Cipulot/CDS/PCB/CDS.kicad_sch

## KiCad design PCB/CDS.kicad_sch (2024-03-03)

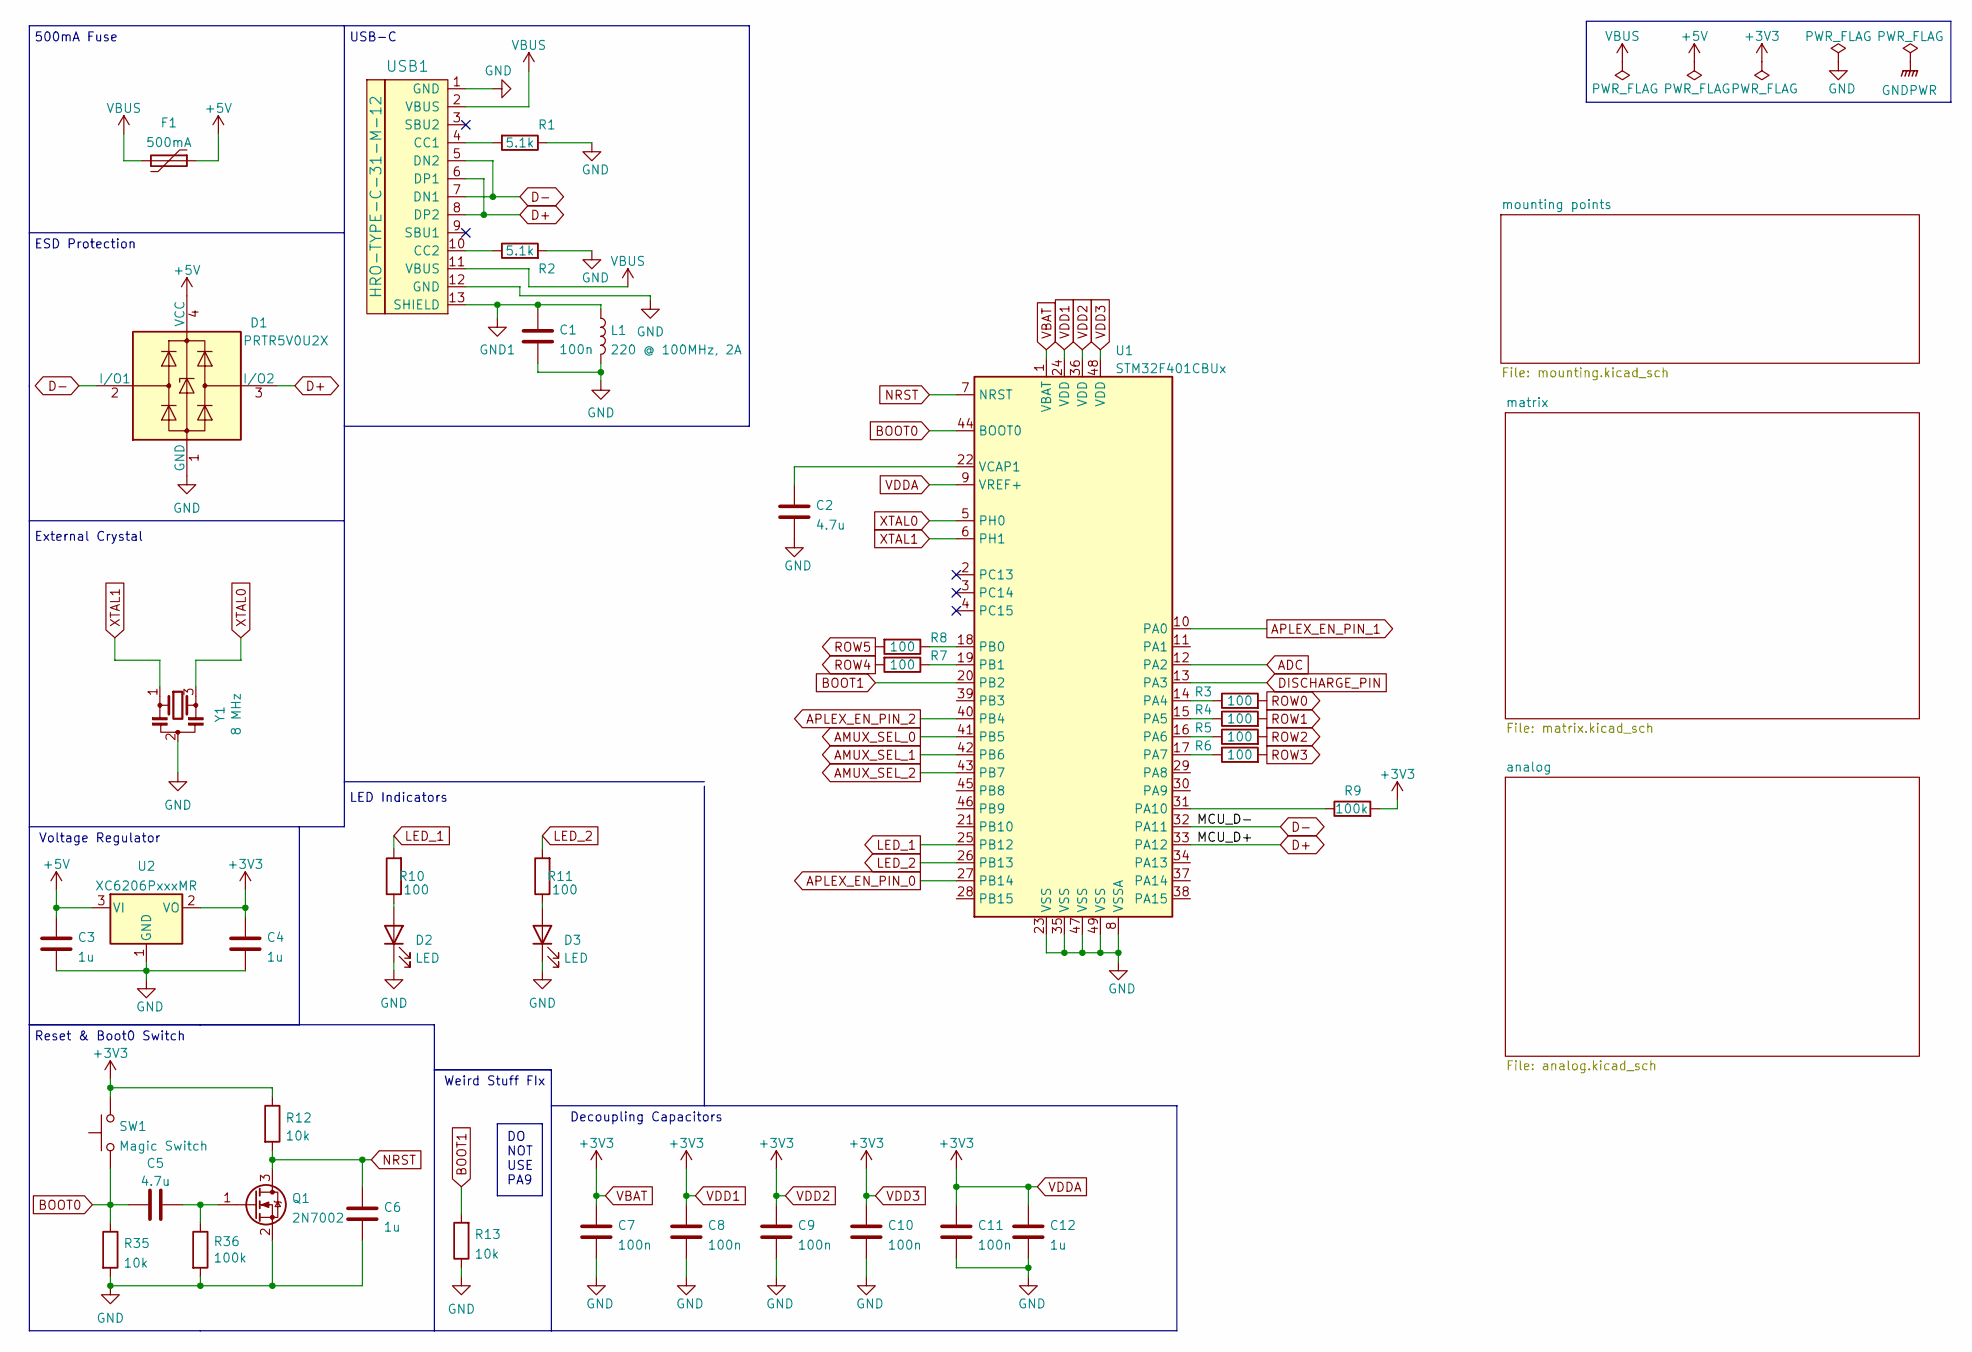
[picture p6: schematic CDS.kicad_sch]

Parts:
C1, C7, C8, C9, C10, C11: 100n; C_0402_1005Metric; LCSC C307331
C2, C5: 4.7u; C_0402_1005Metric; LCSC C23733
C3, C4, C6, C12: 1u; C_0402_1005Metric; LCSC C52923
D1: PRTR5V0U2X; SOT-143; LCSC C2827688
D2, D3: LED; LED_D3.0mm
F1: 500mA; Fuse_0603_1608Metric; LCSC C720073
L1: 220 @ 100MHz, 2A; L_0603_1608Metric; LCSC C85832
Q1: 2N7002; SOT-23; LCSC C8545
R1, R2: 5.1k; R_0402_1005Metric; LCSC C25905
R3, R4, R5, R6, R7, R8, R10, R11: 100; R_0402_1005Metric; LCSC C25076
R9, R36: 100k; R_0402_1005Metric; LCSC C25741
R12, R13, R35: 10k; R_0402_1005Metric; LCSC C25744
SW1: Magic Switch; SW_SPST_TL3342; LCSC C318884
U1: STM32F401CBUx; QFN-48-1EP_7x7mm_P0.5mm_EP5.6x5.6mm; LCSC C118825
U2: XC6206PxxxMR; SOT-23; LCSC C5446
USB1: HRO-TYPE-C-31-M-12; HRO-TYPE-C-31-M-12-Assembly; LCSC C165948
Y1: 8 MHz; Resonator_SMD_Murata_CSTxExxV-3Pin_3.0x1.1mm; LCSC C907975

Connections:
+3V3: C4.1, C7.1, C8.1, C9.1, C10.1, C11.1, C12.1, R9.2, R12.1, SW1.2, U1.1 (VBAT), U1.9 (VREF+), U1.24 (VDD), U1.36 (VDD), U1.48 (VDD), U2.2 (VO)
+5V: C3.1, D1.4 (VCC), F1.1, U2.3 (VI)
ADC: U1.12 (PA2)
AMUX_SEL_0: U1.41 (PB5)
AMUX_SEL_1: U1.42 (PB6)
AMUX_SEL_2: U1.43 (PB7)
APLEX_EN_PIN_0: U1.27 (PB14)
APLEX_EN_PIN_1: U1.10 (PA0)
APLEX_EN_PIN_2: U1.40 (PB4)
BOOT0: C5.1, R35.1, SW1.1, U1.44 (BOOT0)
BOOT1: R13.2, U1.20 (PB2)
D+: D1.3 (I/O2), U1.33 (PA12), USB1.6 (DP1), USB1.8 (DP2)
D-: D1.2 (I/O1), U1.32 (PA11), USB1.5 (DN2), USB1.7 (DN1)
DISCHARGE_PIN: U1.13 (PA3)
GND: C1.2, C2.2, C3.2, C4.2, C6.2, C7.2, C8.2, C9.2, C10.2, C11.2, C12.2, D1.1 (GND), D2.1 (K), D3.1 (K), L1.2, Q1.2 (S), R1.1, R2.2, R13.1, R35.2, R36.2, U1.8 (VSSA), U1.23 (VSS), U1.35 (VSS), U1.47 (VSS), U1.49 (VSS), U2.1 (GND), USB1.1 (GND), USB1.12 (GND), Y1.2
GND1: C1.1, L1.1, USB1.13 (SHIELD)
LED_1: R10.2, U1.25 (PB12)
LED_2: R11.2, U1.26 (PB13)
NRST: C6.1, Q1.3 (D), R12.2, U1.7 (NRST)
unnamed: C2.1, U1.22 (VCAP1)
unnamed: C5.2, Q1.1 (G), R36.1
unnamed: D2.2 (A), R10.1
unnamed: D3.2 (A), R11.1
unnamed: R1.2, USB1.4 (CC1)
unnamed: R2.1, USB1.10 (CC2)
unnamed: R3.1, U1.14 (PA4)
unnamed: R4.1, U1.15 (PA5)
unnamed: R5.1, U1.16 (PA6)
unnamed: R6.1, U1.17 (PA7)
unnamed: R7.1, U1.19 (PB1)
unnamed: R8.1, U1.18 (PB0)
unnamed: R9.1, U1.31 (PA10)
ROW0: R3.2
ROW1: R4.2
ROW2: R5.2
ROW3: R6.2
ROW4: R7.2
ROW5: R8.2
VBUS: F1.2, USB1.2 (VBUS), USB1.11 (VBUS)
XTAL0: U1.5 (PH0), Y1.3
XTAL1: U1.6 (PH1), Y1.1

Notes on the sheet:
DO NOT USE PA9
Voltage Regulator
USB-C
Reset & Boot0 Switch
External Crystal
500mA Fuse
Weird Stuff FIx
Decoupling Capacitors
LED Indicators
ESD Protection
