Cipulot/CDS/PCB/analog.kicad_sch

## KiCad design PCB/analog.kicad_sch (2024-03-03)

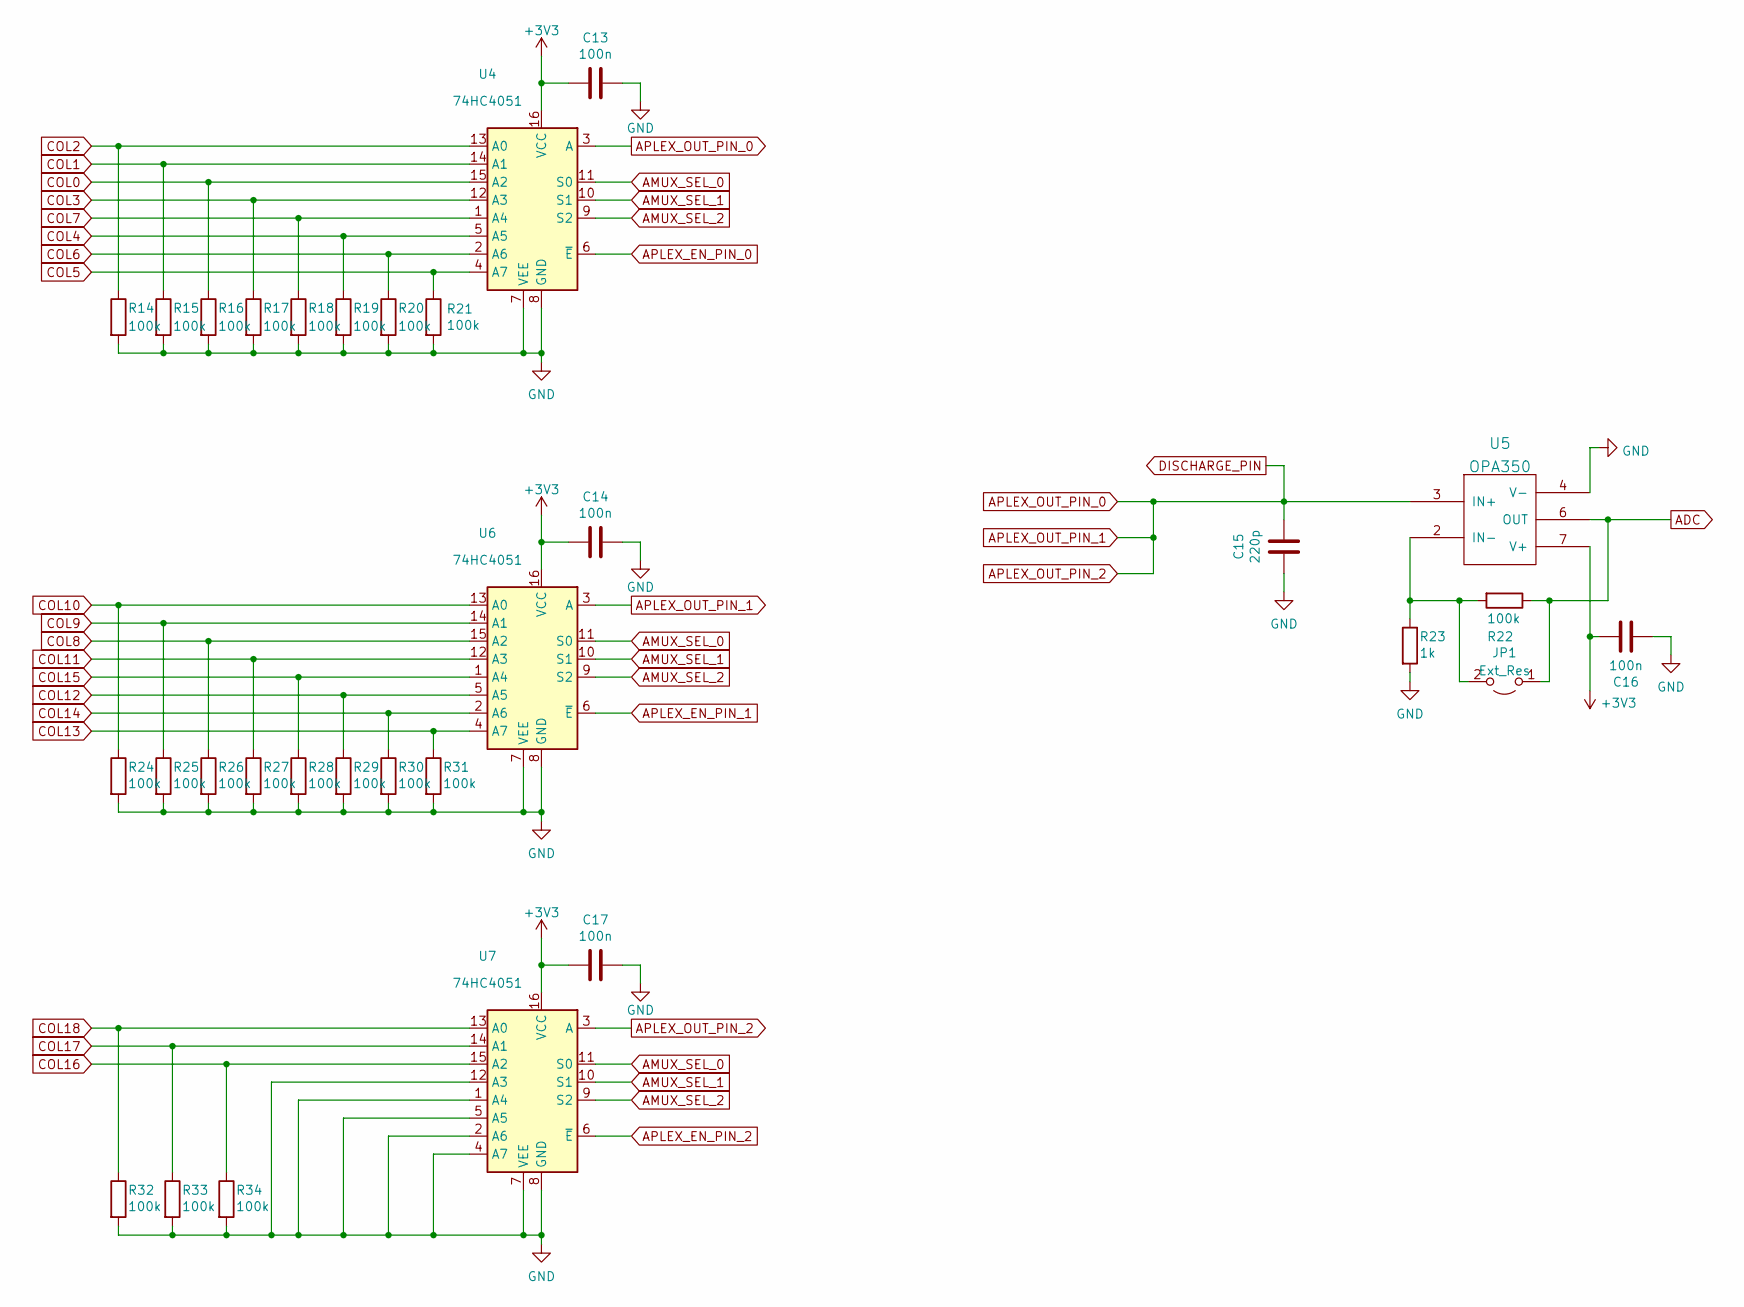
[picture p7: schematic analog.kicad_sch]

Parts:
C13, C14, C16, C17: 100n; C_0402_1005Metric; LCSC C307331
C15: 220p; C_0402_1005Metric; LCSC C1530
JP1: Ext_Res; R_0603_1608Metric_Pad0.98x0.95mm_HandSolder
R14, R15, R16, R17, R18, R19, R20, R21, R22, R24, R25, R26, R27, R28, R29, R30, R31, R32, R33, R34: 100k; R_0402_1005Metric; LCSC C25741
R23: 1k; R_0402_1005Metric; LCSC C11702
U4, U6, U7: 74HC4051; TSSOP16; LCSC C5645
U5: OPA350; SOIC-8_3.9x4.9mm_P1.27mm; LCSC C13388

Connections:
+3V3: C13.2, C14.2, C16.2, C17.2, U4.16 (VCC), U5.7 (V+), U6.16 (VCC), U7.16 (VCC)
ADC: JP1.1 (A), R22.1, U5.6 (OUT)
AMUX_SEL_0: U4.11 (S0), U6.11 (S0), U7.11 (S0)
AMUX_SEL_1: U4.10 (S1), U6.10 (S1), U7.10 (S1)
AMUX_SEL_2: U4.9 (S2), U6.9 (S2), U7.9 (S2)
APLEX_EN_PIN_0: U4.6 (~E)
APLEX_EN_PIN_1: U6.6 (~E)
APLEX_EN_PIN_2: U7.6 (~E)
APLEX_OUT_PIN_0: C15.1, U4.3 (A), U5.3 (IN+), U6.3 (A), U7.3 (A)
COL0: R16.1, U4.15 (A2)
COL1: R15.1, U4.14 (A1)
COL2: R14.1, U4.13 (A0)
COL3: R17.1, U4.12 (A3)
COL4: R19.1, U4.5 (A5)
COL5: R21.1, U4.4 (A7)
COL6: R20.1, U4.2 (A6)
COL7: R18.1, U4.1 (A4)
COL8: R26.1, U6.15 (A2)
COL9: R25.1, U6.14 (A1)
COL10: R24.1, U6.13 (A0)
COL11: R27.1, U6.12 (A3)
COL12: R29.1, U6.5 (A5)
COL13: R31.1, U6.4 (A7)
COL14: R30.1, U6.2 (A6)
COL15: R28.1, U6.1 (A4)
COL16: R34.1, U7.15 (A2)
COL17: R33.1, U7.14 (A1)
COL18: R32.1, U7.13 (A0)
GND: C13.1, C14.1, C15.2, C16.1, C17.1, R14.2, R15.2, R16.2, R17.2, R18.2, R19.2, R20.2, R21.2, R23.2, R24.2, R25.2, R26.2, R27.2, R28.2, R29.2, R30.2, R31.2, R32.2, R33.2, R34.2, U4.7 (VEE), U4.8 (GND), U5.4 (V-), U6.7 (VEE), U6.8 (GND), U7.1 (A4), U7.2 (A6), U7.4 (A7), U7.5 (A5), U7.7 (VEE), U7.8 (GND), U7.12 (A3)
unnamed: JP1.2 (B), R22.2, R23.1, U5.2 (IN-)
