Cipulot/CDS/PCB/mounting.kicad_sch

## KiCad design PCB/mounting.kicad_sch (2024-03-03)

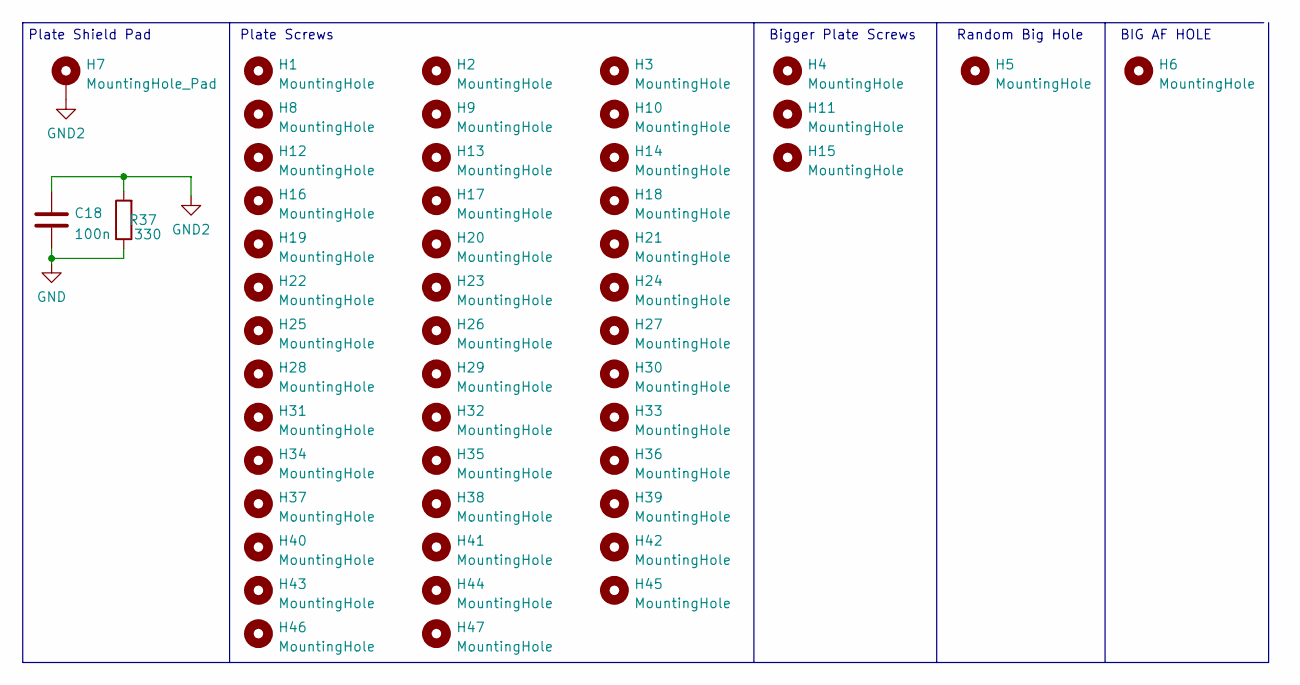
[picture p9: schematic mounting.kicad_sch]

Parts:
C18: 100n; C_0402_1005Metric; LCSC C307331
H1, H2, H3, H8, H9, H10, H12, H13, H14, H16, H17, H18, H19, H20, H21, H22, H23, H24, H25, H26, H27, H28, H29, H30, H31, H32, H33, H34, H35, H36, H37, H38, H39, H40, H41, H42, H43, H44, H45, H46, H47: MountingHole; HOLE_M2_RF
H4, H11, H15: MountingHole; MountingHole_3.5mm
H5: MountingHole; MountingHole_4mm
H6: MountingHole; MountingHole_6.5mm
H7: MountingHole_Pad; MountingHole_2.7mm_M2.5_Pad
R37: 330; R_0402_1005Metric; LCSC C25104

Connections:
GND: C18.2, R37.1
GND2: C18.1, H7.1, R37.2

Notes on the sheet:
BIG AF HOLE
Plate Screws
Random Big Hole
Plate Shield Pad
Bigger Plate Screws
